iboBey333/measure-one/Kicad/Measure_One_Main_Body/Measure_One_Main_Body_Panelized/Measure_One_Main_Body_Panelized_Combined_Top.png

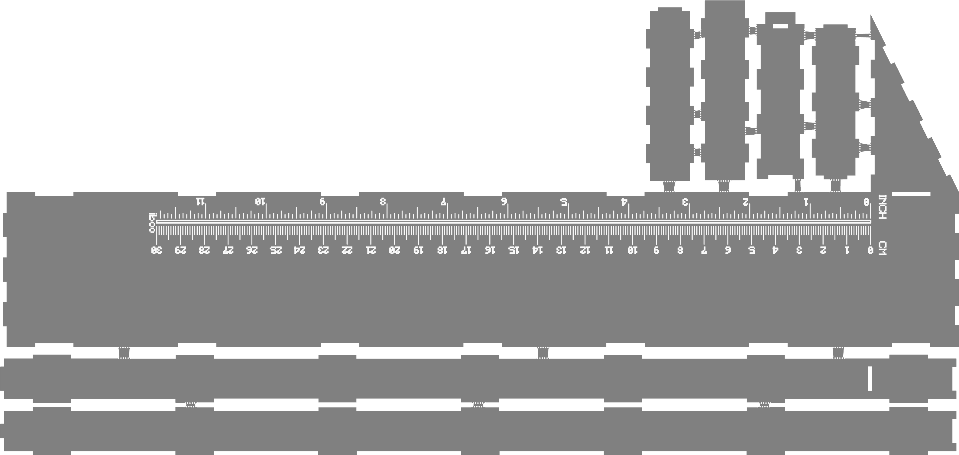
Kicad/Measure_One_Main_Body/Measure_One_Main_Body_Panelized/Measure_One_Main_Body_Panelized_Combined_Top.png
