iboBey333/measure-one/Kicad/Measure_One_Slider/Measure_One_Slider_Panelized/Untitled_Combined_Top.png

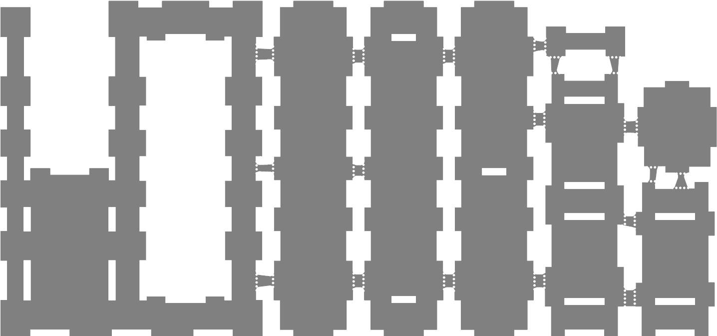
Kicad/Measure_One_Slider/Measure_One_Slider_Panelized/Untitled_Combined_Top.png
