iboBey333/measure-one/Kicad/W_Instructions/Measure_One_Main_Body_W_I/Measure_One_Main_Body_Panelized_W_I/Measure_One_Main_Body_Panelized_W_I_Combined_Top.png

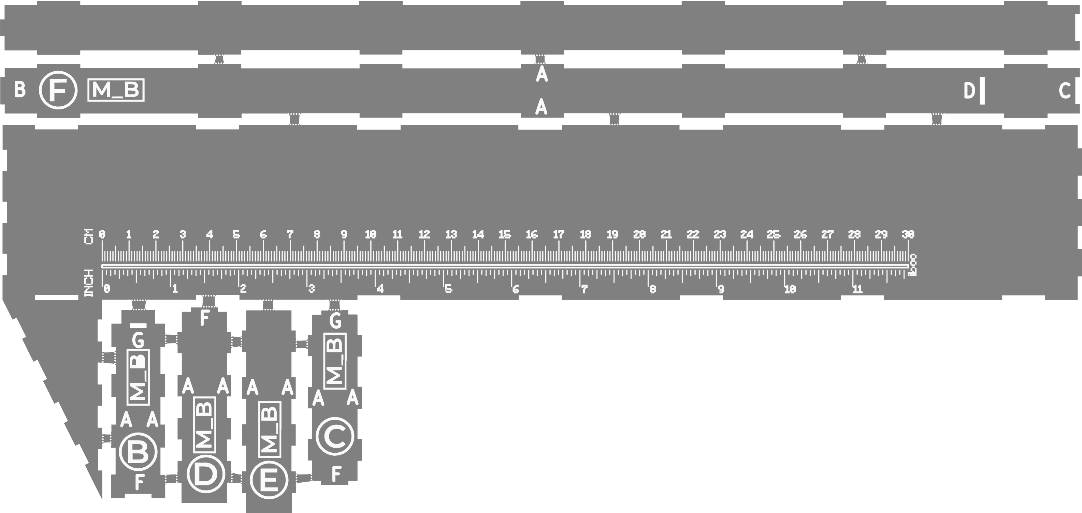
Kicad/W_Instructions/Measure_One_Main_Body_W_I/Measure_One_Main_Body_Panelized_W_I/Measure_One_Main_Body_Panelized_W_I_Combined_Top.png
