iboBey333/measure-one/Kicad/W_Instructions/Measure_One_Slider_Pointer_W_I/Measure_One_Slider_Pointer_Panelized_W_I/Measure_One_Slider_Pointer_Panelized_W_I_Combined_Bottom.png

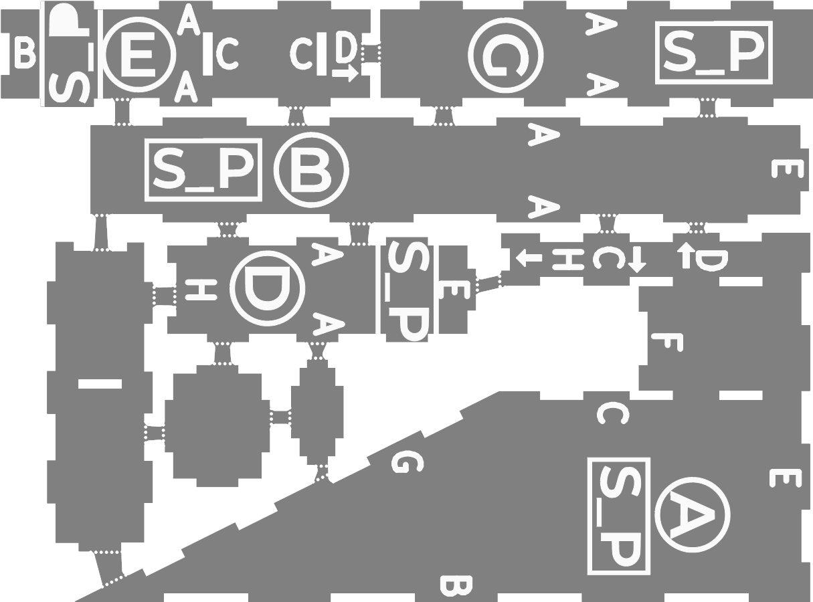
Kicad/W_Instructions/Measure_One_Slider_Pointer_W_I/Measure_One_Slider_Pointer_Panelized_W_I/Measure_One_Slider_Pointer_Panelized_W_I_Combined_Bottom.png
