iboBey333/measure-one/Kicad/W_Instructions/Measure_One_Slider_W_I/Measure_One_Slider_Panelized_W_I/Untitled_Combined_Bottom.png

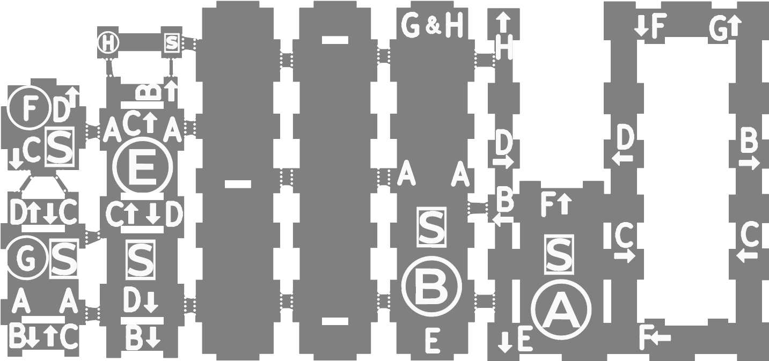
Kicad/W_Instructions/Measure_One_Slider_W_I/Measure_One_Slider_Panelized_W_I/Untitled_Combined_Bottom.png
